timelab/ADEM/people/stmarco/EEPROMclear/EEPROMclear.ino

/*
 * EEPROM Clear
 *
 * Sets all of the bytes of the EEPROM to 0.
 * This example code is in the public domain.

 */

#include <EEPROM.h>

void setup()
{
  EEPROM.begin(512);
  // write a 0 to all 512 bytes of the EEPROM
  for (int i = 0; i < 512; i++)
    EEPROM.write(i, 0);

  // turn the LED on when we're done
  pinMode(5, OUTPUT);
  digitalWrite(5, HIGH);
  EEPROM.end();
}

void loop()
{
}
