timelab/ADEM/people/stmarco/ESPfilesystem/ESPfilesystem.ino

#include "FS.h"

void setup() {
  Serial.begin(115200);

  // always use this to "mount" the filesystem
  bool result = SPIFFS.begin();
  Serial.println("SPIFFS opened: " + result);

  // this opens the file "f.txt" in read-mode
  File f = SPIFFS.open("/f.txt", "r");
  
  if (!f) {
    Serial.println("File doesn't exist yet. Creating it");

    // open the file in write mode
    File f = SPIFFS.open("/f.txt", "w");
    if (!f) {
      Serial.println("file creation failed");
    }
    // now write two lines in key/value style with  end-of-line characters
    f.println("ssid=abc");
    f.println("password=123455secret");
  } else {
    // we could open the file
    while(f.available()) {
      //Lets read line by line from the file
      String line = f.readStringUntil('\n');
      Serial.println(line);
    }
  f.close();
  }
    File i = SPIFFS.open("/index.html", "r");
    if(!i) {
      Serial.println("index file niet gevonden");
    }
    else {
      while(i.available()) {
        String line2 = i.readStringUntil('\n');
        Serial.println(line2);
    }
//    Serial.println("The end");
  i.close();
  }
}

void loop() {
  // nothing to do for now, this is just a simple test

}
