timelab/ADEM/people/kavers1/i2c-gps-nav/registers.h

///////////////////////////////////////////////////////////////////////////////////////////////////
// I2C GPS NAV registers
///////////////////////////////////////////////////////////////////////////////////////////////////
//
#define I2C_GPS_STATUS_00                            00 //(Read only)
        #define I2C_GPS_STATUS_NEW_DATA       0x01      // New data is available (after every GGA frame)
        #define I2C_GPS_STATUS_2DFIX          0x02      // 2dfix achieved
        #define I2C_GPS_STATUS_3DFIX          0x04      // 3dfix achieved
        #define I2C_GPS_STATUS_WP_REACHED     0x08      // Active waypoint has been reached (not cleared until new waypoint is set)
        #define I2C_GPS_STATUS_NUMSATS        0xF0      // Number of sats in view

#define I2C_GPS_COMMAND                              01 // (write only)
        #define I2C_GPS_COMMAND_POSHOLD       0x01      // Start position hold at the current gps positon
        #define I2C_GPS_COMMAND_START_NAV     0x02      // get the WP from the command and start navigating toward it
        #define I2C_GPS_COMMAND_SET_WP        0x03      // copy current position to given WP      
        #define I2C_GPS_COMMAND_UPDATE_PIDS   0x04      // update PI and PID controllers from the PID registers, this must be called after a pid register is changed
        #define I2C_GPS_COMMAND_NAV_OVERRIDE  0x05      // do not nav since we tring to controll the copter manually (not implemented yet)
        #define I2C_GPS_COMMAND_STOP_NAV      0x06      // Stop navigation (zeroes out nav_lat and nav_lon
        #define I2C_GPS_COMMAND__7            0x07
        #define I2C_GPS_COMMAND__8            0x08      
        #define I2C_GPS_COMMAND__9            0x09
        #define I2C_GPS_COMMAND__a            0x0a
        #define I2C_GPS_COMMAND__b            0x0b
        #define I2C_GPS_COMMAND__c            0x0c
        #define I2C_GPS_COMMAND__d            0x0d
        #define I2C_GPS_COMMAND__e            0x0e
        #define I2C_GPS_COMMAND__f            0x0f

        #define I2C_GPS_COMMAND_WP_MASK       0xF0       // Waypoint number

#define I2C_GPS_WP_REG                              02   // Waypoint register (Read only)
        #define I2C_GPS_WP_REG_ACTIVE_MASK    0x0F       // Active Waypoint lower 4 bits
        #define I2C_GPS_WP_REG_PERVIOUS_MASK  0xF0       // pervious Waypoint upper 4 bits
        
#define I2C_GPS_REG_VERSION                         03   // Version of the I2C_NAV SW uint8_t
#define I2C_GPS_REG_RES2                            04   // reserved for future use (uint8_t)
#define I2C_GPS_REG_RES3                            05   // reserved for future use (uint8_t)
#define I2C_GPS_REG_RES4                            06   // reserved for future use (uint8_t)


#define I2C_GPS_LOCATION                            07   // current location 8 byte (lat, lon) int32_t
#define I2C_GPS_NAV_LAT                             15   // Desired banking towards north/south int16_t
#define I2C_GPS_NAV_LON                             17   // Desired banking toward east/west    int16_t
#define I2C_GPS_WP_DISTANCE                         19   // Distance to current WP in cm uint32
#define I2C_GPS_WP_TARGET_BEARING                   23   // bearing towards current wp 1deg = 1000 int16_t
#define I2C_GPS_NAV_BEARING                         25   // crosstrack corrected bearing towards current wp 1deg = 1000 int16_t
#define I2C_GPS_HOME_TO_COPTER_BEARING              27   // bearing from home to copter 1deg = 1000 int16_t
#define I2C_GPS_DISTANCE_TO_HOME                    29   // distance to home in m int16_t
        
#define I2C_GPS_GROUND_SPEED                        31   // GPS ground speed in m/s*100 (uint16_t)      (Read Only)
#define I2C_GPS_ALTITUDE                            33   // GPS altitude in meters (uint16_t)           (Read Only)
#define I2C_GPS_GROUND_COURSE			    35   // GPS ground course (uint16_t)
#define I2C_GPS_RES1                                37   // reserved for future use (uint16_t)
#define I2C_GPS_TIME                                39   // UTC Time from GPS in hhmmss.sss * 100 (uint32_t)(unneccesary precision) (Read Only)

//Writeable registers from here

#define I2C_GPS_CROSSTRACK_GAIN                     43    // Crosstrack gain *100 (1 - 0.01 100 - 1) uint8_t
#define I2C_GPS_SPEED_MIN                           44    // Minimum navigation speed cm/s uint8_t
#define I2C_GPS_SPEED_MAX                           45    // Maximum navigation speed cm/s uint16_t
#define I2C_GPS_RESERVED                            47    // Reserved for future use
#define I2C_GPS_WP_RADIUS                           49    // Radius of the wp in cm, within this radius we consider the wp reached (uint16_t)

#define I2C_GPS_NAV_FLAGS                           51    // Controls various functions of the I2C-GPS-NAV module
        #define I2C_NAV_FLAG_GPS_FILTER          0x80     // If this bit set GPS coordinates are filtered via a 5 element moving average filter
        #define I2C_NAV_FLAG_LOW_SPEED_D_FILTER  0x40     // If speed below .5m/s ignore D term in POSHOLD_RATE, this supposed to filter out noise

#define I2C_GPS_HOLD_P                              52    // poshold_P  *100 uint16_t
#define I2C_GPS_HOLD_I                              53    // poshold_I  *100 uint16_t
#define I2C_GPS_HOLD_IMAX                           54    // poshold_IMAX *1 uint8_t

#define I2C_GPS_HOLD_RATE_P                         55    // poshold_rate_P  *10 uint16_t
#define I2C_GPS_HOLD_RATE_I                         56    // poshold_rate_I  *100 uint16_t
#define I2C_GPS_HOLD_RATE_D                         57    // poshold_rate_D  *1000 uint16_t
#define I2C_GPS_HOLD_RATE_IMAX                      58    // poshold_rate_IMAX *1 uint8_t

#define I2C_GPS_NAV_P                               59    // nav_P  *10 uint16_t
#define I2C_GPS_NAV_I                               60    // nav_I  *100 uint16_t
#define I2C_GPS_NAV_D                               61    // nav_D  *1000 uint16_t
#define I2C_GPS_NAV_IMAX                            62    // nav_IMAX *1 uint8_t

#define I2C_GPS_WP0                                 63   //Waypoint 0 used for RTH location      (R/W)
#define	I2C_GPS_WP1		                    74
#define	I2C_GPS_WP2		                    85
#define	I2C_GPS_WP3		                    96
#define	I2C_GPS_WP4		                    107
#define	I2C_GPS_WP5		                    118
#define	I2C_GPS_WP6		                    129
#define	I2C_GPS_WP7		                    140
#define	I2C_GPS_WP8		                    151
#define	I2C_GPS_WP9		                    162
#define	I2C_GPS_WP10		                    173
#define	I2C_GPS_WP11		                    184
#define	I2C_GPS_WP12		                    195
#define	I2C_GPS_WP13		                    206
#define	I2C_GPS_WP14		                    217
#define	I2C_GPS_WP15		                    228



#define I2C_GPS_SONAR_DISTANCE					239			//uint16_t sonar distance in cm




///////////////////////////////////////////////////////////////////////////////////////////////////
// End register definition 
///////////////////////////////////////////////////////////////////////////////////////////////////
