timelab/ADEM/people/stmarco/WiFiAPmetSPIFFS/foot.h

unsigned char foot_html[] = {
  0x3c, 0x2f, 0x64, 0x69, 0x76, 0x3e, 0x0a, 0x3c, 0x2f, 0x62, 0x6f, 0x64,
  0x79, 0x3e, 0x0a, 0x3c, 0x2f, 0x68, 0x74, 0x6d, 0x6c, 0x3e, 0x0a
};
unsigned int foot_html_len = 23;
