timelab/ADEM/people/stmarco/WiFiAPmetSPIFFS/index.h

unsigned char index_html[] = {
  0x3c, 0x64, 0x69, 0x76, 0x3e, 0x0a, 0x20, 0x20, 0x20, 0x20, 0x3c, 0x68,
  0x33, 0x3e, 0x41, 0x44, 0x45, 0x4d, 0x3c, 0x2f, 0x68, 0x33, 0x3e, 0x0a,
  0x20, 0x20, 0x20, 0x20, 0x3c, 0x70, 0x3e, 0x47, 0x65, 0x65, 0x66, 0x20,
  0x68, 0x69, 0x65, 0x72, 0x6f, 0x6e, 0x64, 0x65, 0x72, 0x20, 0x6a, 0x65,
  0x20, 0x6e, 0x65, 0x74, 0x77, 0x65, 0x72, 0x6b, 0x20, 0x67, 0x65, 0x67,
  0x65, 0x76, 0x65, 0x6e, 0x73, 0x20, 0x69, 0x6e, 0x3c, 0x2f, 0x70, 0x3e,
  0x0a, 0x20, 0x20, 0x20, 0x20, 0x3c, 0x69, 0x6e, 0x70, 0x75, 0x74, 0x20,
  0x74, 0x79, 0x70, 0x65, 0x3d, 0x22, 0x74, 0x65, 0x78, 0x74, 0x22, 0x20,
  0x69, 0x64, 0x3d, 0x22, 0x73, 0x73, 0x69, 0x64, 0x22, 0x20, 0x70, 0x6c,
  0x61, 0x63, 0x65, 0x68, 0x6f, 0x6c, 0x64, 0x65, 0x72, 0x3d, 0x22, 0x53,
  0x53, 0x49, 0x44, 0x22, 0x3e, 0x0a, 0x20, 0x20, 0x20, 0x20, 0x3c, 0x69,
  0x6e, 0x70, 0x75, 0x74, 0x20, 0x74, 0x79, 0x70, 0x65, 0x3d, 0x22, 0x74,
  0x65, 0x78, 0x74, 0x22, 0x20, 0x69, 0x64, 0x3d, 0x22, 0x75, 0x73, 0x65,
  0x72, 0x22, 0x20, 0x70, 0x6c, 0x61, 0x63, 0x65, 0x68, 0x6f, 0x6c, 0x64,
  0x65, 0x72, 0x3d, 0x22, 0x75, 0x73, 0x65, 0x72, 0x6e, 0x61, 0x6d, 0x65,
  0x20, 0x28, 0x6f, 0x70, 0x74, 0x69, 0x6f, 0x6e, 0x61, 0x6c, 0x29, 0x22,
  0x3e, 0x0a, 0x20, 0x20, 0x20, 0x20, 0x3c, 0x69, 0x6e, 0x70, 0x75, 0x74,
  0x20, 0x74, 0x79, 0x70, 0x65, 0x3d, 0x22, 0x74, 0x65, 0x78, 0x74, 0x22,
  0x20, 0x69, 0x64, 0x3d, 0x22, 0x6b, 0x65, 0x79, 0x22, 0x20, 0x70, 0x6c,
  0x61, 0x63, 0x65, 0x68, 0x6f, 0x6c, 0x64, 0x65, 0x72, 0x3d, 0x22, 0x6e,
  0x65, 0x74, 0x77, 0x6f, 0x72, 0x6b, 0x20, 0x6b, 0x65, 0x79, 0x22, 0x3e,
  0x0a, 0x20, 0x20, 0x20, 0x20, 0x3c, 0x69, 0x6e, 0x70, 0x75, 0x74, 0x20,
  0x74, 0x79, 0x70, 0x65, 0x3d, 0x22, 0x73, 0x75, 0x62, 0x6d, 0x69, 0x74,
  0x22, 0x20, 0x76, 0x61, 0x6c, 0x75, 0x65, 0x3d, 0x22, 0x53, 0x75, 0x62,
  0x6d, 0x69, 0x74, 0x22, 0x3e, 0x0a, 0x20, 0x20, 0x20, 0x20, 0x3c, 0x70,
  0x3e, 0x3c, 0x61, 0x20, 0x68, 0x72, 0x65, 0x66, 0x3d, 0x22, 0x73, 0x63,
  0x61, 0x6e, 0x2e, 0x68, 0x74, 0x6d, 0x6c, 0x22, 0x3e, 0x4f, 0x66, 0x20,
  0x64, 0x6f, 0x65, 0x20, 0x65, 0x65, 0x6e, 0x20, 0x73, 0x63, 0x61, 0x6e,
  0x20, 0x76, 0x61, 0x6e, 0x20, 0x68, 0x65, 0x74, 0x20, 0x6e, 0x65, 0x74,
  0x77, 0x65, 0x72, 0x6b, 0x3c, 0x2f, 0x61, 0x3e, 0x3c, 0x2f, 0x70, 0x3e,
  0x0a, 0x3c, 0x2f, 0x64, 0x69, 0x76, 0x3e, 0x0a
};
unsigned int index_html_len = 368;
