timelab/ADEM/people/dagwieers/buzzer_test/buzzer_test.ino

/*
 * This file is part of the ADEM project.
 *
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
 * Copyright 2016 Dag Wieers
 *
 */

#include <buzzer_passive.h>

#define BUZZER_PIN 5
#define SERIAL_BAUD 74880

PassiveBuzzer buzzer;

void setup() {
    Serial.begin(SERIAL_BAUD);
    Serial.println();
    Serial.println("Serial communication... OK");

    buzzer.begin();

    Serial.println();
    Serial.println("Press \"a\" for alarm sound.");
    Serial.println("Press \"c\" for collect sound.");
    Serial.println("Press \"C\" for config sound.");
    Serial.println("Press \"s\" for start sound.");
    Serial.println("Press \"w\" for warning sound.");
    Serial.println("Press 1-8 for notes.");
    Serial.println();
}

void loop() {

    delay(10);

    if (Serial.available() > 0) {
        char c = Serial.read();
        if (c != '\n' and c != '\r') {
            Serial.print("Key "); Serial.print(c); Serial.println(" is pressed. ");
            switch (c) {
                case 'a': buzzer.alarm_sound(); break;
                case 'c': buzzer.collect_sound(); break;
                case 'C': buzzer.config_sound(); break;
                case 's': buzzer.start_sound(); break;
                case 'w': buzzer.warning_sound(); break;
                case '1': buzzer.playnote(NOTE_C, 100); break;
                case '2': buzzer.playnote(NOTE_D, 100); break;
                case '3': buzzer.playnote(NOTE_E, 100); break;
                case '4': buzzer.playnote(NOTE_F, 100); break;
                case '5': buzzer.playnote(NOTE_G, 100); break;
                case '6': buzzer.playnote(NOTE_A, 100); break;
                case '7': buzzer.playnote(NOTE_B, 100); break;
                case '8': buzzer.playnote(NOTE_CC, 100); break;
                default: Serial.println("No action.");
            }
        }
    }
}
