timelab/ADEM/people/stmarco/WiFiAPmetSPIFFS/scan.h

unsigned char scan_html[] = {
  0x20, 0x20, 0x20, 0x20, 0x3c, 0x68, 0x33, 0x3e, 0x47, 0x65, 0x76, 0x6f,
  0x6e, 0x64, 0x65, 0x6e, 0x20, 0x6e, 0x65, 0x74, 0x77, 0x65, 0x72, 0x6b,
  0x65, 0x6e, 0x3c, 0x2f, 0x68, 0x33, 0x3e, 0x0a
};
unsigned int scan_html_len = 32;
